pavel-bilous/LM1876_mute/sim-LTSpice/time_delayed_NOT_rev2.asc

C1: cap; 22µF
D1: zener; UMZ5_1N
D2: LED; NSCW100
D3: diode; 1N4148
M1: nmos; 2N7002
R2: res; 10K
R3: res; 10K
R4: res; 100K
V1: voltage; PULSE(0 25 2 0.1 5 6 1 1); Rser=1
Named nets: 0, Vsupply
logic NOT gate
LM1876 mute pin
5V zener regulator
Positive rail supply from LM1876
Vbrkd = 5V
Iave = 0.03A
Rmin = Vin-Vz / Imax
Rmin = [25V - 5V] / 0.1A
RC time delay
.tran 15s startup
C1 discharge diode (after power off)
